slowbro/lldp_stick/src/display.cpp

#include "display.h"

char *display_buffer[8];
int display_line_start[8] = {0};
int display_buffer_size[8] = {0};
uint8_t display_buffer_top = 0;
uint32_t display_last_animation, display_last_header_animation = 0;
Adafruit_SSD1306 display(OLED_WIDTH, OLED_HEIGHT, &Wire, PIN_OLED_RESET);

/**
 * Initialize the OLED display and display buffer.
 *
 */
void display_init(){
    pinMode(PIN_OLED_RESET, OUTPUT);

    display.begin(SSD1306_SWITCHCAPVCC, 0x3C);

    display.dim(settings.oled_dim);

    display.clearDisplay();
    display.setTextSize(1);
    display.setCursor(32,32);
    display.setTextColor(WHITE);
    display.print(F("Booting..."));
    display.display();

    for(int i=0;i<8;i++){
        display_buffer[i] = (char *)malloc(1);
        display_buffer[i][0] = '\0';
        display_buffer_size[i] = 1;
    }
}

/**
 * Clear the display buffer and reset line starts.
 *
 */
void display_clear_buffer(){
    for(int i=0;i<8;i++){
        display_buffer[i] = (char *)realloc(display_buffer[i], 1);
        memset(display_buffer[i], '\0', 1);
        display_line_start[i] = 0;
        display_buffer_size[i] = 1;
    }
}

/**
 * Add a "string" to the display buffer.
 *
 */
void display_set_buffer_line(uint8_t line, const char *str){
    int len = strlen(str);
    display_buffer[line] = (char *)realloc(display_buffer[line], len + 1);
    memcpy(display_buffer[line], str, len);
    display_buffer[line][len] = '\0';
    display_buffer_size[line] = len;
}

/**
 * Add a "string" to the display buffer, except centered this time.
 *
 */
void display_set_buffer_line_centered(uint8_t line, const char *str){
    int len = strlen(str);
    int spaces = (OLED_MAXLEN - len) / 2;
    display_buffer[line] = (char *)realloc(display_buffer[line], spaces + len + 1);
    if(spaces > 0)
        sprintf(display_buffer[line], "%*c", spaces, ' ');
    memcpy(display_buffer[line]+spaces, str, len);
    display_buffer[line][spaces+len] = '\0';
    display_buffer_size[line] = spaces+len;
}

/**
 * Add a "string" to the display buffer based on some arbitrary data's start and length (i.e. PDUInfo).
 *
 */
void display_set_buffer_line(uint8_t line, uint8_t *data, uint16_t start, uint16_t len) {
    display_buffer[line] = (char *)realloc(display_buffer[line], len + 1);
    memcpy(display_buffer[line], &data[start], len);
    display_buffer[line][len] = '\0';
    display_buffer_size[line] = len;
}

/**
 * Add a "string" to the display buffer based on some arbitrary data's start and length (i.e. PDUInfo),
 * but this time with a statically defined prefix.
 *
 */
void display_set_buffer_line(uint8_t line, const char *prefix, uint8_t *data, uint16_t start, uint16_t len) {
    int prefix_len = strlen(prefix);
    display_buffer[line] = (char *)realloc(display_buffer[line], prefix_len + len + 1);
    memcpy(display_buffer[line], prefix, prefix_len);
    memcpy(display_buffer[line]+prefix_len, &data[start], len);
    display_buffer[line][prefix_len+len] = '\0';
    display_buffer_size[line] = prefix_len+len;
}

/**
 * Add a "string" to the display buffer based on some arbitrary data's start and length (i.e. PDUInfo),
 * but this time with a statically defined prefix - integer input edition.
 *
 */
void display_set_buffer_line_int(uint8_t line, const char *prefix, uint8_t *data, uint16_t start, uint16_t len) {
    int prefix_len = strlen(prefix);

    // this is so jank, and i have no idea if it works
    // for TTLs > 120 :|
    char *l = (char *)malloc(2);
    int int_data = 0;
    memcpy(&int_data, &data[start], len);
    int_data = int_data >> 4*(sizeof(int_data)-len);
    int size = snprintf(l, 2, "%d", int_data);
    if(size > 2){
        l = (char *)realloc(l, size+1);
        snprintf(l, size+1, "%d", int_data);
    }

    display_buffer[line] = (char *)realloc(display_buffer[line], prefix_len + size + 1);
    memcpy(display_buffer[line], prefix, prefix_len);
    memcpy(display_buffer[line]+prefix_len, l, size);
    display_buffer[line][prefix_len+size] = '\0';
    display_buffer_size[line] = prefix_len+size;

    free(l);
}

/**
 * Draw the header.
 *
 */
void display_set_header(){
    display.fillRect(0, 0, display.width(), 7, WHITE);
    display.setTextSize(1);
    display.setTextColor(BLACK);
    if(ble_connected){
        // bluetooth logo: super shitty edition
        // s2g this was easier than drawing a BMP
        display.drawTriangle(3, 4, 3, 0, 5, 2, BLACK);
        display.drawTriangle(3, 7, 3, 2, 5, 4, BLACK);
        display.drawLine(1, 1, 3, 3, BLACK);
        display.drawLine(1, 5, 3, 3, BLACK);
    }

    display.println();

    // battery sillhouette
    display.fillRect(display.width()-20, 1, 18, 5, BLACK);
    display.fillRect(display.width()-2, 3, 1, 1, BLACK);

    // battery bars
    float bv = battery_voltage();
    if(bv > 3.2) {
        display.fillRect(display.width()-18, 2, 2, 3, WHITE);
    }

    if(bv > 3.5) {
        display.fillRect(display.width()-14, 2, 2, 3, WHITE);
    }

    if(bv > 3.8) {
        display.fillRect(display.width()-10, 2, 2, 3, WHITE);
    }

    if(bv > 4.0) {
        display.fillRect(display.width()-6, 2, 2, 3, WHITE);
    }
}

/**
 * Draw the footer.
 *
 */
void display_set_footer(){
    display.setTextSize(1);
    display.setTextColor(WHITE);
    if(display_buffer_length() > DISPLAY_LINES){
        display.println("< More        Menu >");
    } else {
        display.println("              Menu >");
    }
}

/**
 * Draw the whole display.
 *
 */
void display_print(){
    char buf[OLED_MAXLEN+1];

    display.clearDisplay();
    display.setCursor(0, 0);

    display_set_header();

    display.setTextSize(1);
    display.setTextColor(WHITE);

    // display lines, potentially scrolling longer ones
    for(int i = display_buffer_top;i<display_buffer_top+DISPLAY_LINES;i++){
        memset(buf, '\0', sizeof(buf));
        int len = strlen(display_buffer[i]);
        if(len <= OLED_MAXLEN){
            // just display the line as-is
            memcpy(&buf, display_buffer[i], len);
            buf[len] = '\0';
        } else {
            // scroll the line slowly to display all text
            memcpy(&buf, &display_buffer[i][display_line_start[i]], OLED_MAXLEN);
            buf[OLED_MAXLEN] = '\0';

            if(millis() - display_last_animation > (display_line_start[i]==0 ? (DISPLAY_SCROLL_DELAY*4*settings.text_scroll_multiplier) : (DISPLAY_SCROLL_DELAY*settings.text_scroll_multiplier)) ){
                display_last_animation = millis();
                if(++display_line_start[i] > len){
                    display_line_start[i] = 0;
                }
            }
        }
        display.println(buf);
    }

    display_set_footer();

    display.display();
}

/**
 * Advance the display(ed) lines, assuming there are lines to advance to.
 *
 */
void display_buffer_advance(){
    // reset the animation timer so newly added lines don't immediately start to animate
    display_last_animation = millis();
    if(display_buffer_length() > OLED_LINES)
        display_buffer_top++;
    if(display_buffer_top > display_buffer_length()-1)
        display_buffer_top = 0;
}

/**
 * Return the length of the display buffer based on strlen()
 *
 */
uint8_t display_buffer_length(){
    uint8_t len = 0;
    for(uint8_t i=0;i<8;i++){
        if(strlen(display_buffer[i]) != 0)
            len++;
    }

    return len;
}
