slowbro/lldp_stick/src/lldp.h

#ifndef LLDP_H
#define LLDP_H

#include <stdint.h>
#include <Arduino.h>

struct PDUInfo {

    // the packet
    uint8_t data[1514];

    // TLV 1: Chassis ID
    uint16_t ChassisIdStart;
    uint8_t ChassisIdSubtype;
    uint16_t ChassisIdLength;

    // TLV 2: Port ID
    uint16_t PortIdStart;
    uint8_t PortIdSubtype;
    uint16_t PortIdLength;

    // TLV 3: TTL
    uint16_t TTLStart;
    uint8_t TTLLength;

    // TLV 4: Port Description
    uint16_t PortDescriptionStart;
    uint16_t PortDescriptionLength;

    // TLV 5: System Name
    uint16_t SystemNameStart;
    uint16_t SystemNameLength;

    // TLV 6: System Description
    uint16_t SystemDescriptionStart;
    uint16_t SystemDescriptionLength;

    // TLV 7: System Capabilities
    uint16_t SystemCapabilitiesStart;
    uint16_t SystemCapabilitiesLength;

    // TLV 8: Management Address
    uint16_t ManagementAddressStart;
    uint16_t ManagementAddressLength;

};

struct TLV_Org {

    // TLV 127
    uint8_t derp;

};

void lldp_process(uint8_t *, uint16_t, PDUInfo *);
void lldp_set_defaults(PDUInfo *);

#endif
