slowbro/lldp_stick/src/network.cpp

#include "network.h"
#include "setting.h"
#include "config.h"

byte network_mac[6];
uint8_t network_buffer[1514];
bool got_lldp = false;

Wiznet5500 w5500(PIN_WIZ_CS);

void network_init(){
    pinMode(PIN_WIZ_RESET, OUTPUT);
    digitalWrite(PIN_WIZ_RESET, HIGH);
    // give the wiznet a bit to initialize
    delay(500);
    w5500.begin(settings.mac_address);
}

void network_generate_mac(byte *dest){
    byte mac[6];

    randomSeed(analogRead(PIN_VDIV));
    for(uint8_t i=0;i<6;i++){
        mac[i] = random(0, 255);
    }

    memcpy(dest, &mac, sizeof(byte)*6);
}
