slowbro/lldp_stick/src/network.h

#ifndef NETWORK_H
#define NETWORK_H

#include <Arduino.h>
#include <network/w5500.h>

extern uint8_t network_buffer[1514];
extern bool got_lldp;

extern Wiznet5500 w5500;

void network_init();
void network_generate_mac(byte *);

#endif
